ElectronicCats/Badge-AppsecPnw-2024/firmware/main/modules/bitmaps.h

#ifndef BITMAPS_H
#define BITMAPS_H

/**
 * @brief Badge logo bitmap
 *
 * width: 64 pixels
 * height: 64 pixels
 */
static unsigned char bitmap_badge_logo[] = {
    0x00, 0x00, 0x00, 0x00, 0x00, 0x00, 0x00, 0x00, 0x7f, 0xff, 0xff, 0xff,
    0xff, 0xff, 0xff, 0xff, 0x7f, 0xff, 0xff, 0xff, 0xff, 0xff, 0xff, 0xfe,
    0x7f, 0xff, 0xff, 0xff, 0xff, 0xff, 0xff, 0xfe, 0x7f, 0xff, 0xff, 0xff,
    0xff, 0xff, 0xff, 0xff, 0x78, 0x00, 0x00, 0x00, 0x00, 0x00, 0x00, 0x1f,
    0x78, 0x00, 0x00, 0x00, 0x00, 0x00, 0x00, 0x1f, 0x78, 0x81, 0xff, 0xfe,
    0x00, 0x00, 0x00, 0x1e, 0x78, 0xff, 0xff, 0xff, 0xff, 0xff, 0xff, 0x9e,
    0x78, 0xff, 0xff, 0xff, 0xff, 0xff, 0xff, 0x9e, 0x78, 0xff, 0xff, 0xff,
    0xff, 0xf8, 0x7f, 0x9e, 0x78, 0xff, 0xff, 0xff, 0xff, 0xe7, 0x9f, 0x9e,
    0x78, 0xff, 0xff, 0xff, 0xff, 0xcf, 0xcf, 0x9e, 0x78, 0xff, 0xff, 0xff,
    0xff, 0xdf, 0xe7, 0x9e, 0x78, 0xff, 0xff, 0xff, 0xff, 0xbb, 0xf7, 0x9e,
    0x78, 0xff, 0xff, 0xfe, 0x7f, 0xbf, 0xf7, 0x9e, 0x78, 0xff, 0xff, 0xfc,
    0x1f, 0xbd, 0x77, 0x9e, 0x78, 0xff, 0xff, 0xf0, 0x0f, 0xbf, 0x77, 0x9e,
    0x78, 0xff, 0xff, 0xe0, 0x03, 0xdf, 0x67, 0x9e, 0x78, 0xff, 0xff, 0x86,
    0x61, 0xcf, 0xcf, 0x9e, 0x78, 0xff, 0xff, 0x0e, 0x78, 0xe3, 0x1f, 0x9e,
    0x78, 0xff, 0xfc, 0x3e, 0x7c, 0x38, 0x7f, 0x9e, 0x78, 0xff, 0xf8, 0x7e,
    0x7f, 0x1f, 0xff, 0x9e, 0x78, 0xff, 0xf1, 0xfe, 0x7f, 0x01, 0xff, 0x1e,
    0x78, 0xff, 0xc3, 0xfe, 0x3f, 0x8e, 0xff, 0x9e, 0x78, 0xff, 0x87, 0xf8,
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
    0x01, 0xe7, 0xff, 0xf8, 0x01, 0xff, 0xff, 0xf8, 0x03, 0xe8, 0xff, 0xfc,
    0x07, 0xe0, 0xff, 0xfe, 0x1f, 0xff, 0xff, 0xfe, 0x1f, 0xff, 0xff, 0xfe,
    0x00, 0x00, 0x00, 0x00, 0x00, 0x00, 0x00, 0x00};

#endif  // BITMAPS_H
